whowechina/iidx_teeny/cad/iidx_keycap_teeny.stl

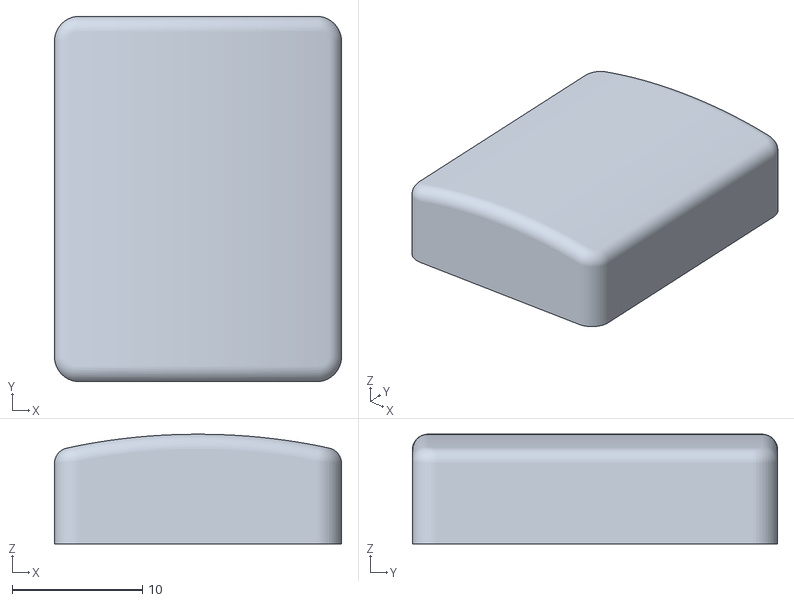
[picture p23: CAD file, 2023-05-01]
cad/iidx_keycap_teeny.stl
22.0 x 28.0 x 8.40
