whowechina/iidx_teeny/PCB/Keyboard/3dmodels/WS2812B.step

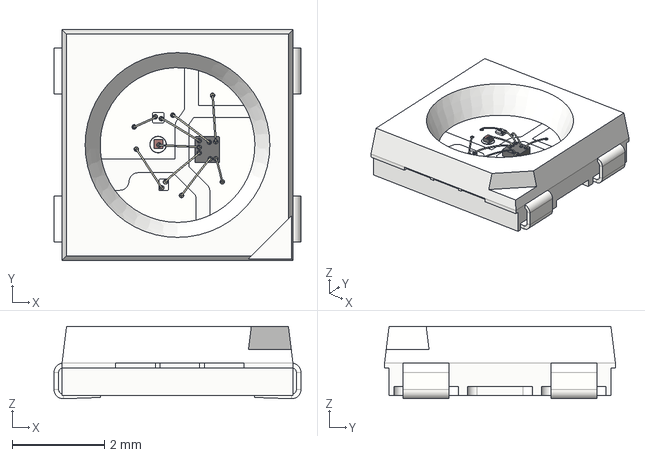
[picture p24: CAD file, 2023-05-01]
PCB/Keyboard/3dmodels/WS2812B.step
5.35 x 5.00 x 1.57 mm
