whowechina/iidx_teeny/Production/3DPrint/Keyboard Teeny - Panel.stl

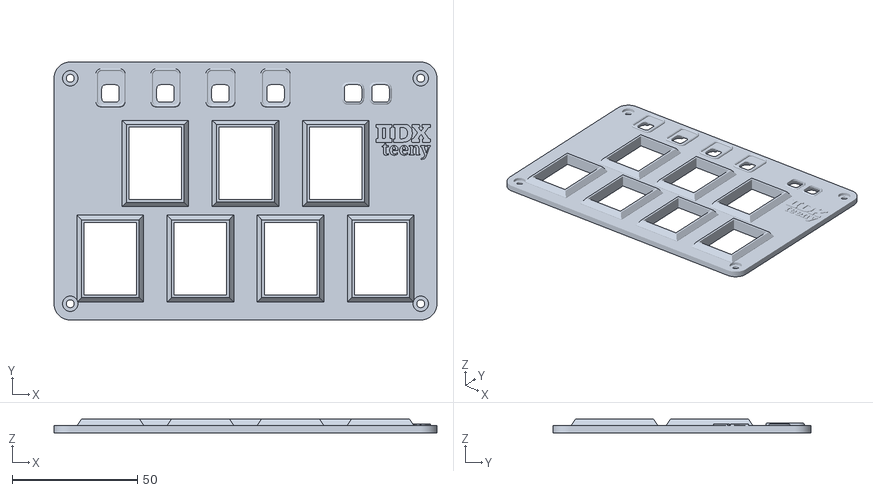
[picture p25: CAD file, 2024-12-18]
Production/3DPrint/Keyboard Teeny - Panel.stl
153.2 x 103.2 x 5.80
