whowechina/iidx_teeny/cad/nsk6804.stl

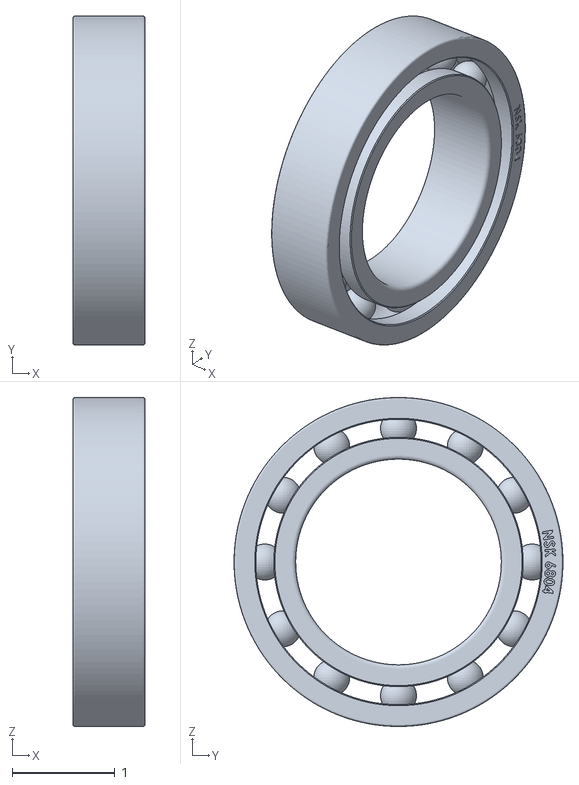
[picture p26: CAD file, 2023-05-01]
cad/nsk6804.stl
0.7 x 3.20 x 3.20
