whowechina/iidx_teeny/PCB/Keyboard/3dmodels/User Library-WS2812-2020.step

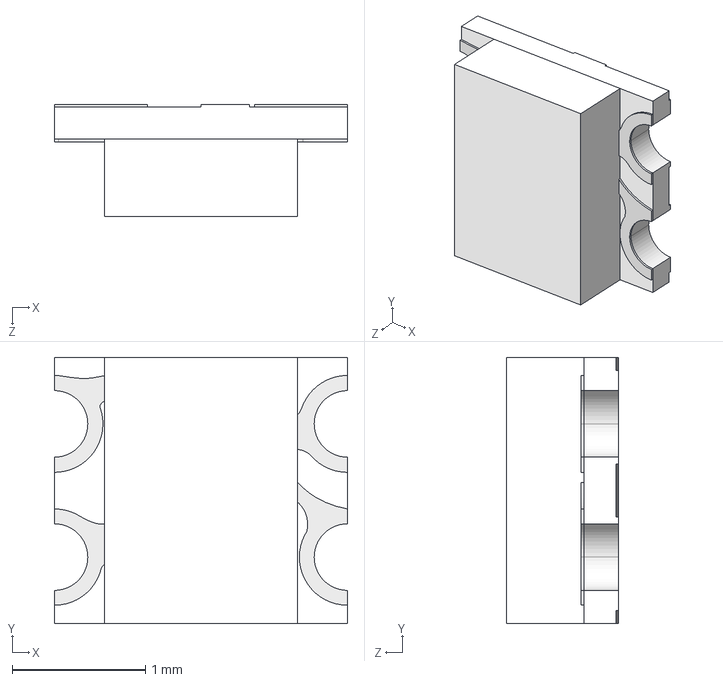
[picture p27: CAD file, 2023-05-01]
PCB/Keyboard/3dmodels/User Library-WS2812-2020.step
2.20 x 2.00 x 0.84 mm
