whowechina/iidx_teeny/cad/tt_led_ring_180.stl

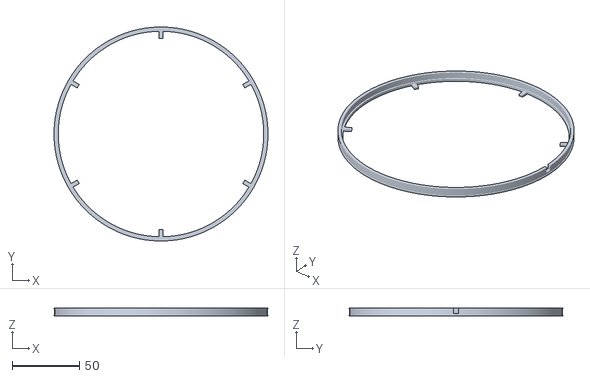
[picture p28: CAD file, 2023-05-01]
cad/tt_led_ring_180.stl
159.0 x 159.0 x 6.18
