whowechina/iidx_teeny/PCB/Keyboard/3dmodels/WS2812-0807.STEP

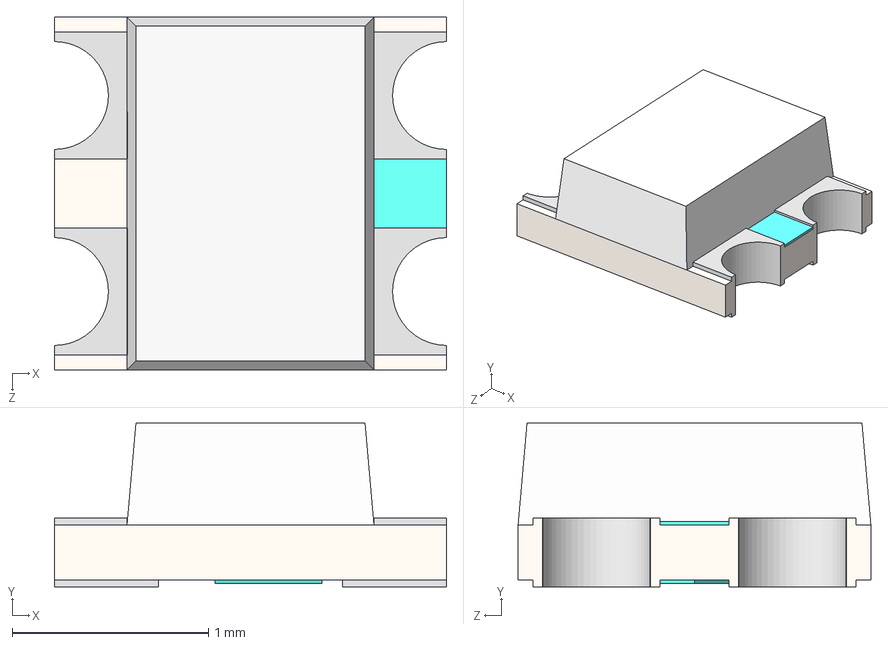
[picture p29: CAD file, 2023-05-01]
PCB/Keyboard/3dmodels/WS2812-0807.STEP
2.00 x 0.835 x 1.80 mm
