whowechina/iidx_teeny/Production/3DPrint/Turntable Teeny - Base.stl

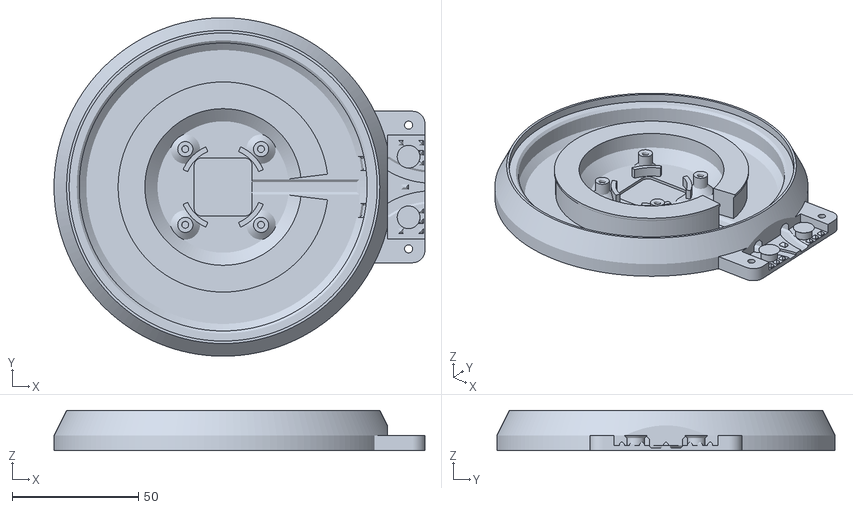
[picture p30: CAD file, 2024-12-18]
Production/3DPrint/Turntable Teeny - Base.stl
146.9 x 134.0 x 16.0
