whowechina/iidx_teeny/cad/keycap_frame_aux.stl

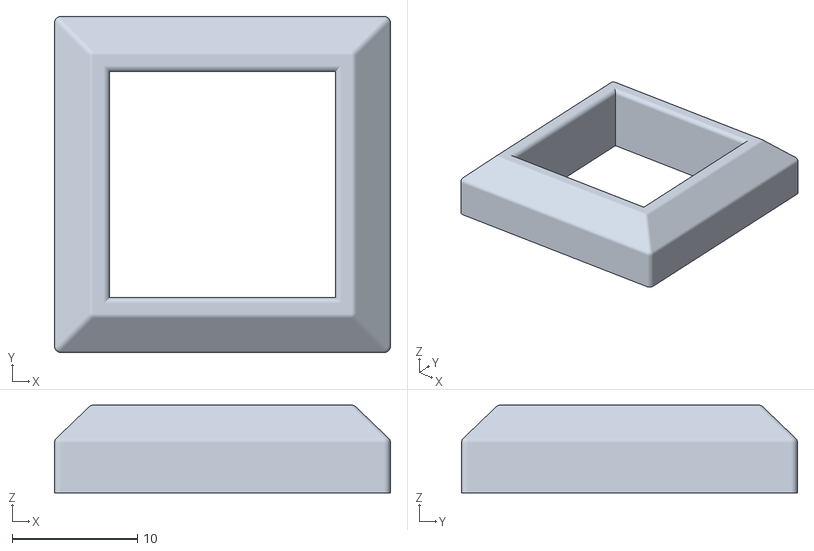
[picture p31: CAD file, 2023-05-01]
cad/keycap_frame_aux.stl
26.8 x 26.8 x 7.00
