whowechina/iidx_teeny/PCB/Keyboard/3dmodels/Magnetic Pogo Connector 5 Pin (F).STEP

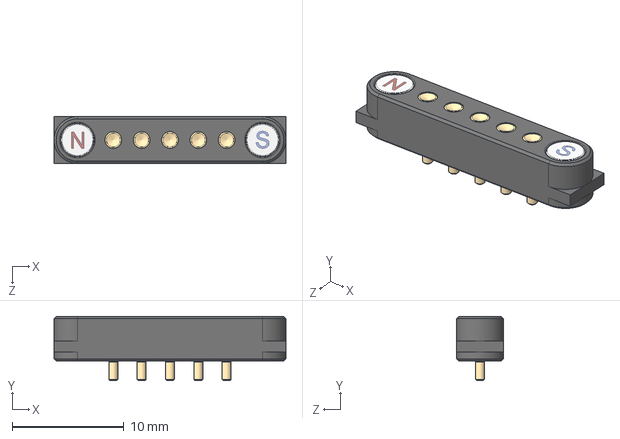
[picture p32: CAD file, 2023-05-01]
PCB/Keyboard/3dmodels/Magnetic Pogo Connector 5 Pin (F).STEP
20.8 x 5.75 x 4.20 mm
