whowechina/iidx_teeny/Production/3DPrint/Keyboard Teeny - Base_1P.stl

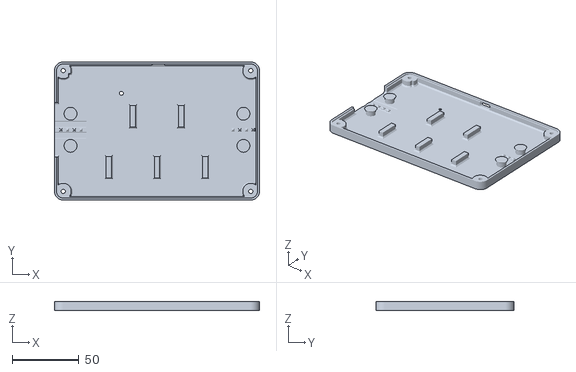
[picture p33: CAD file, 2024-12-18]
Production/3DPrint/Keyboard Teeny - Base_1P.stl
153.2 x 103.2 x 7.00
