whowechina/iidx_teeny/PCB/Keyboard/3dmodels/User Library-PTS645SL95SMTR92-LFS.STEP

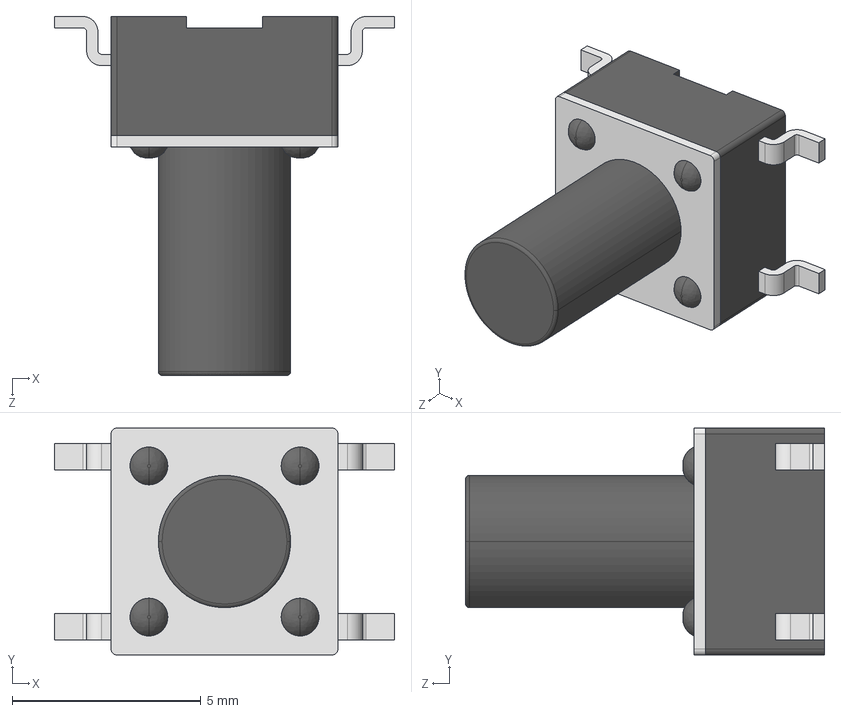
[picture p34: CAD file, 2023-05-01]
PCB/Keyboard/3dmodels/User Library-PTS645SL95SMTR92-LFS.STEP
9.00 x 6.00 x 9.50 mm
