whowechina/iidx_teeny/Production/3DPrint/Keycap Teeny - Choc V2.stl

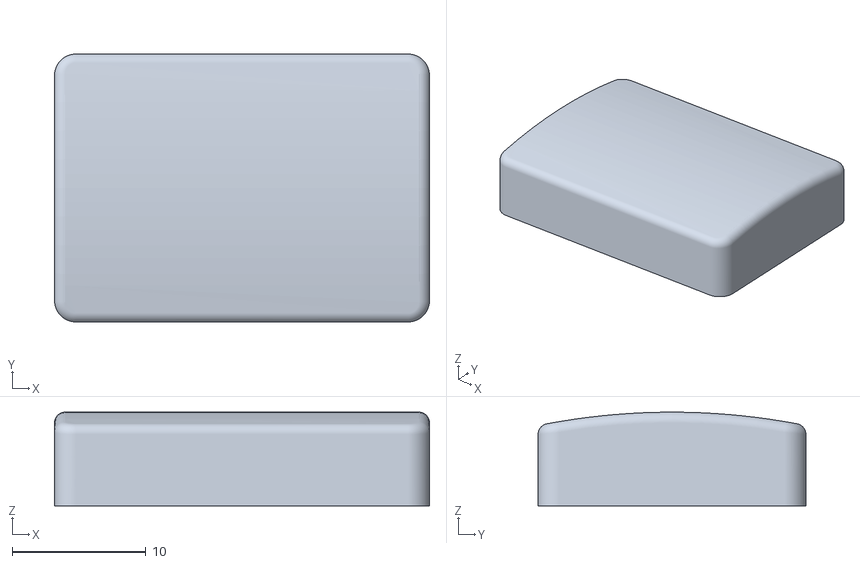
[picture p35: CAD file, 2024-12-18]
Production/3DPrint/Keycap Teeny - Choc V2.stl
28.0 x 20.0 x 7.00
