whowechina/iidx_teeny/cad/beatmania_iidx.stl

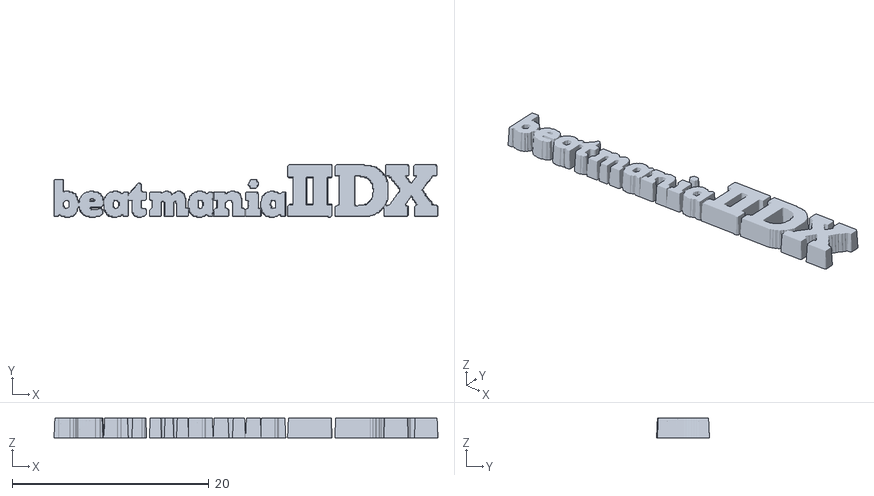
[picture p36: CAD file, 2023-05-01]
cad/beatmania_iidx.stl
39.0 x 5.38 x 2.00
