whowechina/iidx_teeny/PCB/Keyboard/3dmodels/EVQ-P1D05M.stp

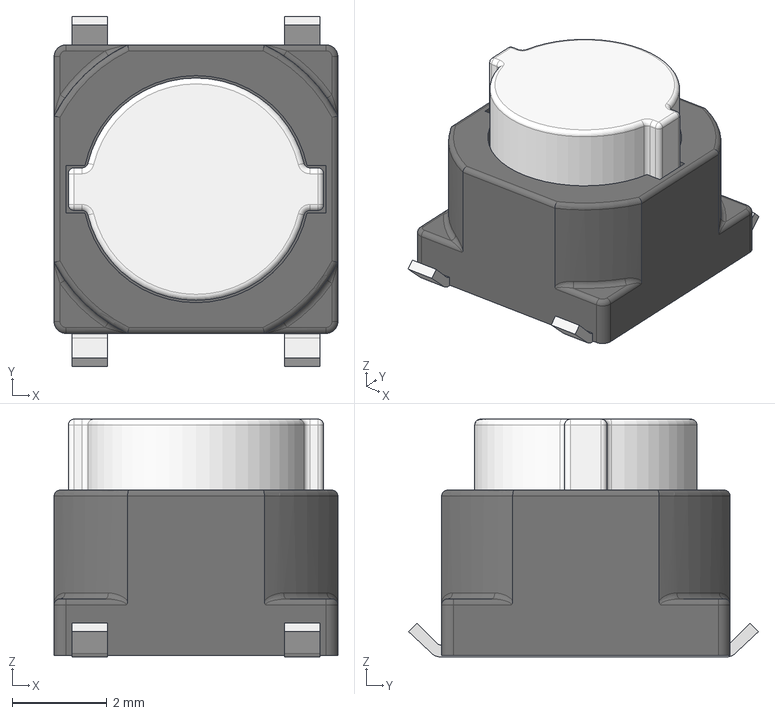
[picture p37: CAD file, 2023-05-01]
PCB/Keyboard/3dmodels/EVQ-P1D05M.stp
6.00 x 7.40 x 5.03 mm
