whowechina/iidx_teeny/PCB/Keyboard/3dmodels/WS2812-2020.STEP

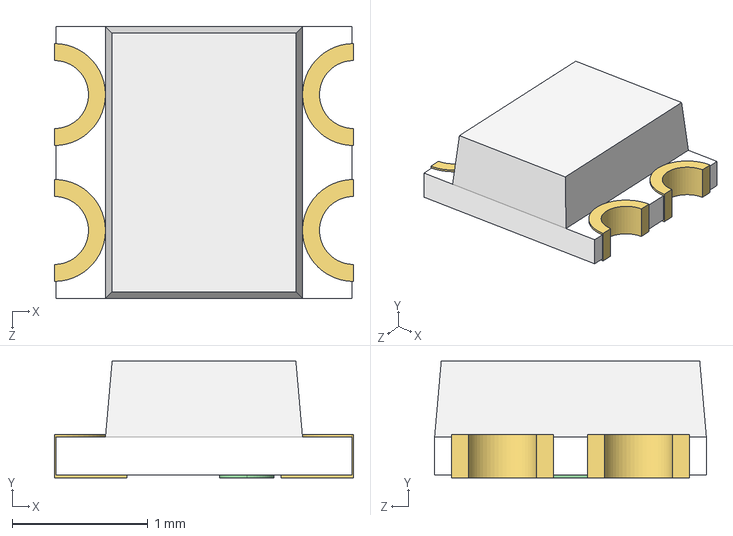
[picture p38: CAD file, 2023-05-01]
PCB/Keyboard/3dmodels/WS2812-2020.STEP
2.20 x 0.86 x 2.00 mm
