whowechina/iidx_teeny/Production/3DPrint/teeny_bottom_P2.stl

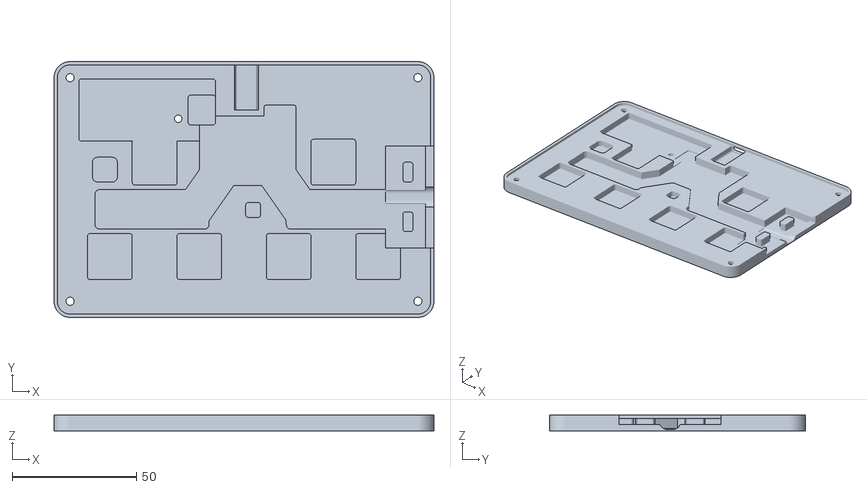
[picture p39: CAD file, 2024-02-12]
Production/3DPrint/teeny_bottom_P2.stl
153.0 x 103.0 x 6.40
