whowechina/iidx_teeny/cad/skf6805.stl

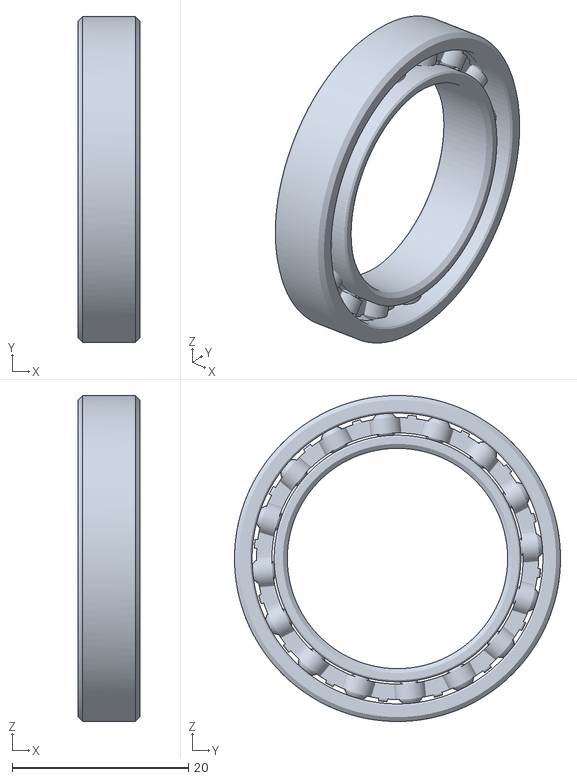
[picture p40: CAD file, 2023-05-01]
cad/skf6805.stl
7.00 x 37.0 x 37.0
