whowechina/iidx_teeny/PCB/Keyboard/3dmodels/SW_Hotswap_Kailh_MX.stp

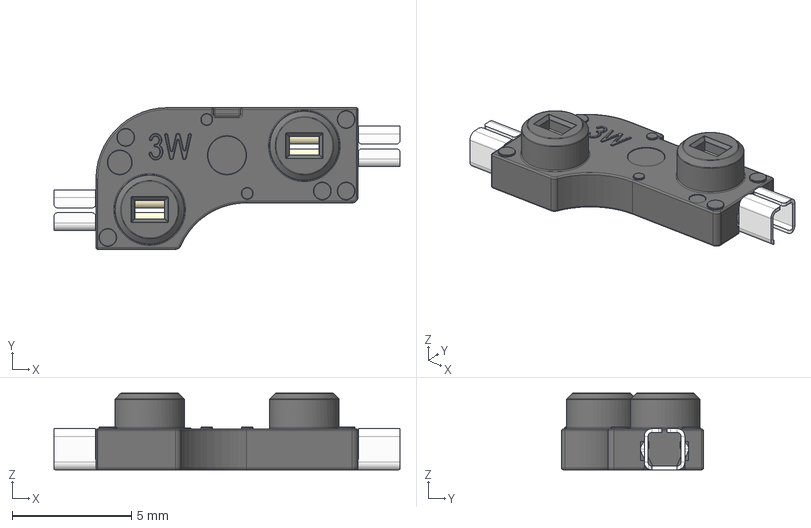
[picture p41: CAD file, 2023-05-01]
PCB/Keyboard/3dmodels/SW_Hotswap_Kailh_MX.stp
14.5 x 5.95 x 3.22 mm
