whowechina/iidx_teeny/cad/iidx_tt v1.stl

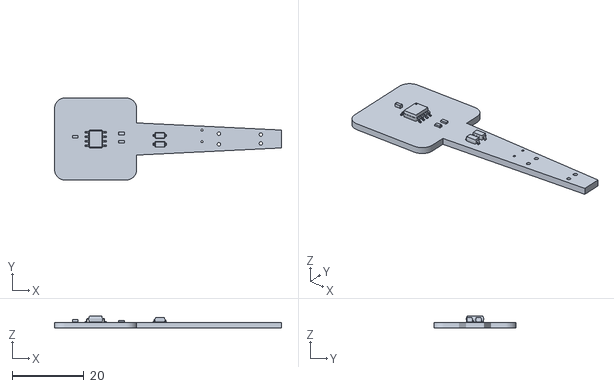
[picture p42: CAD file, 2023-05-01]
cad/iidx_tt v1.stl
63.5 x 23.0 x 3.40
