whowechina/iidx_teeny/PCB/Keyboard/3dmodels/Magnetic Pogo Connector 5 Pin (Type 2).STEP

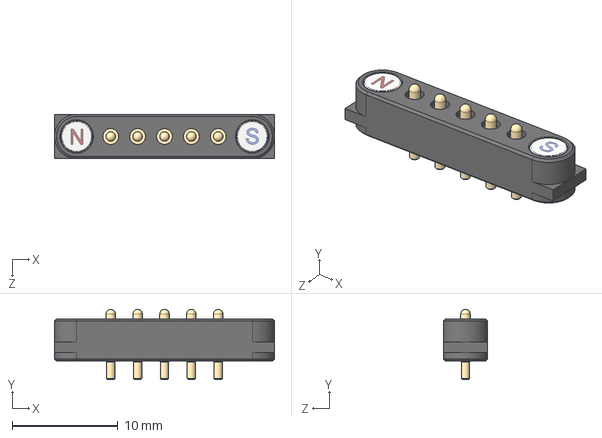
[picture p43: CAD file, 2023-05-01]
PCB/Keyboard/3dmodels/Magnetic Pogo Connector 5 Pin (Type 2).STEP
20.8 x 6.65 x 4.20 mm
