whowechina/iidx_teeny/Production/3DPrint/teeny_hinge_cover.stl

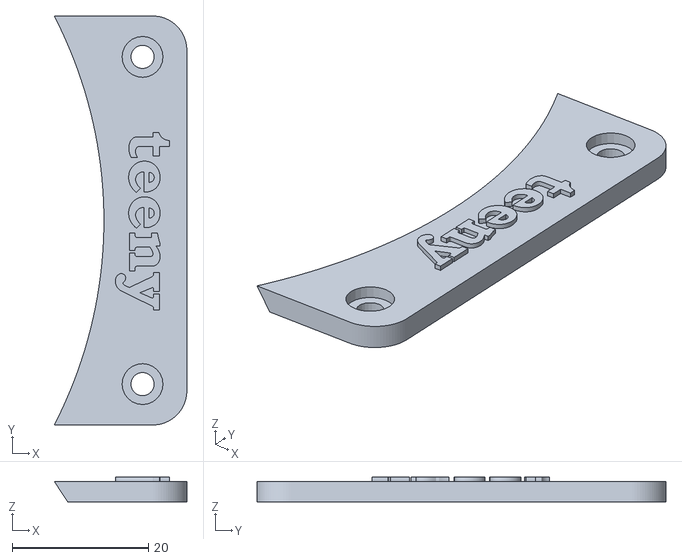
[picture p44: CAD file, 2023-07-23]
Production/3DPrint/teeny_hinge_cover.stl
19.5 x 60.0 x 3.60
