whowechina/iidx_teeny/PCB/Keyboard/3dmodels/SW_Kailh_Choc_V1.stp

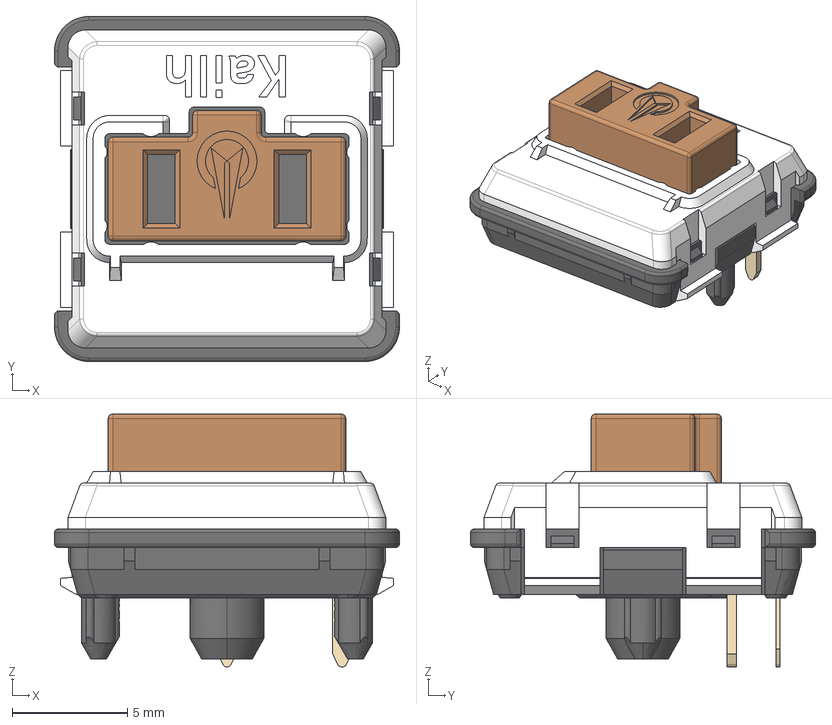
[picture p45: CAD file, 2023-05-01]
PCB/Keyboard/3dmodels/SW_Kailh_Choc_V1.stp
15.0 x 15.0 x 11.0 mm
