whowechina/iidx_teeny/Production/3DPrint/teeny_top.stl

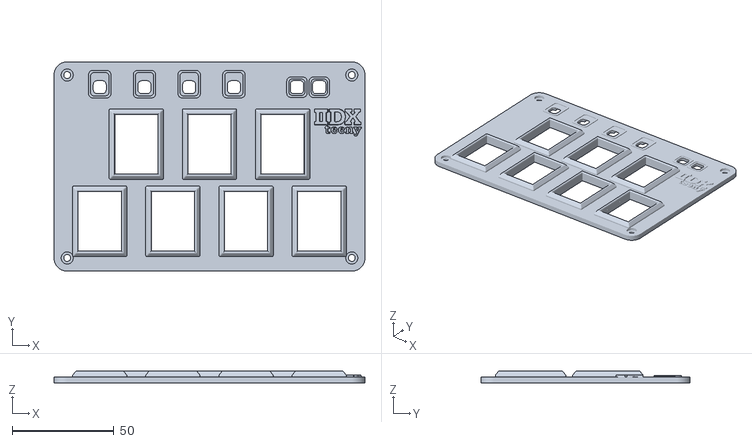
[picture p46: CAD file, 2023-05-26]
Production/3DPrint/teeny_top.stl
153.0 x 103.0 x 5.86
