whowechina/iidx_teeny/Production/3DPrint/teeny_keycap.stl

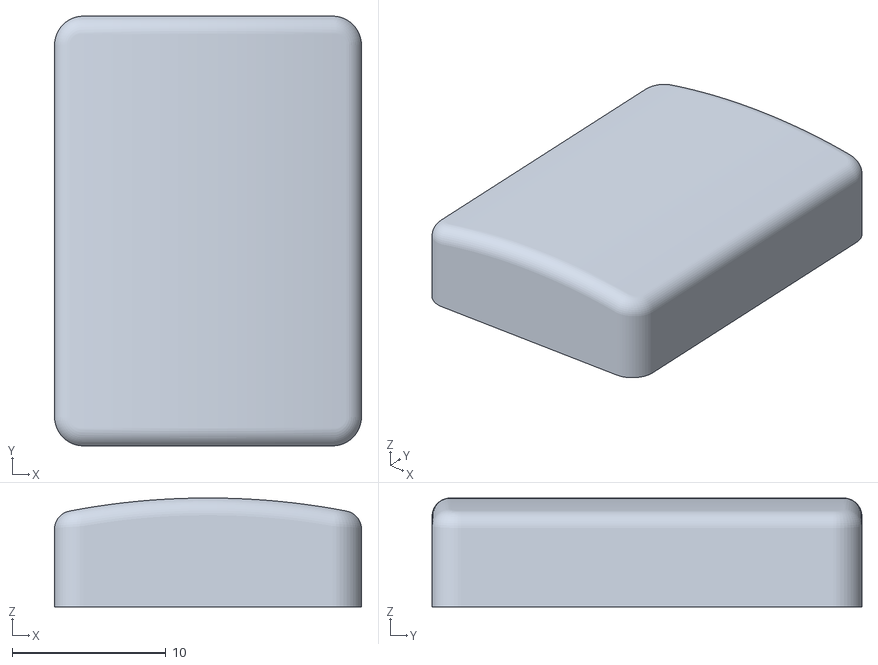
[picture p47: CAD file, 2023-05-21]
Production/3DPrint/teeny_keycap.stl
20.0 x 28.0 x 7.10
