whowechina/iidx_teeny/Production/3DPrint/teeny_disc.stl

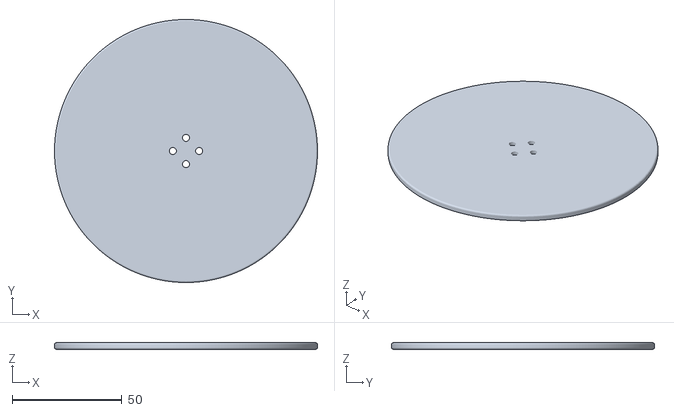
[picture p49: CAD file, 2023-05-14]
Production/3DPrint/teeny_disc.stl
120.0 x 120.0 x 2.99
