whowechina/iidx_teeny/PCB/Keyboard/3dmodels/SMD WS2812B-3535.step

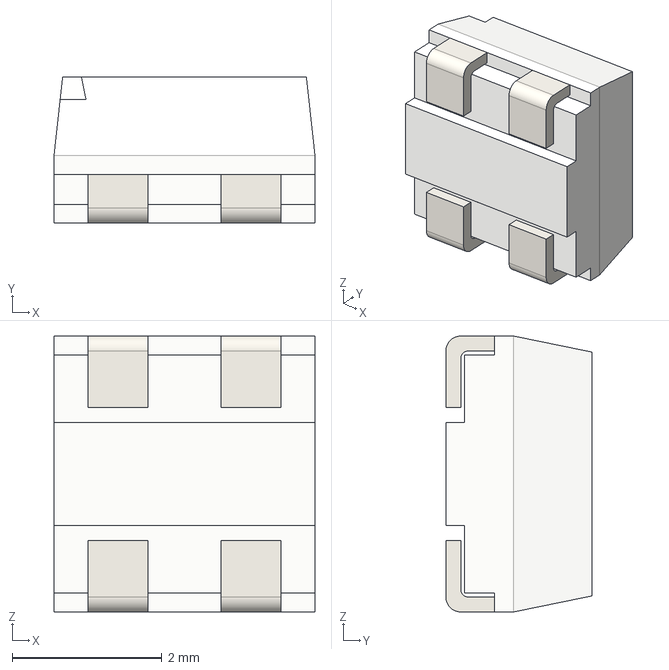
[picture p50: CAD file, 2023-05-01]
PCB/Keyboard/3dmodels/SMD WS2812B-3535.step
3.48 x 1.95 x 3.68 mm
