whowechina/iidx_teeny/Production/3DPrint/teeny_shaft.stl

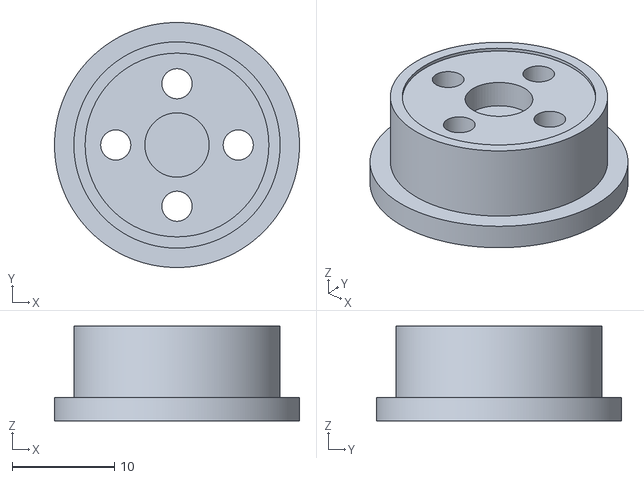
[picture p51: CAD file, 2023-05-14]
Production/3DPrint/teeny_shaft.stl
24.0 x 24.0 x 9.30
