whowechina/iidx_teeny/Production/3DPrint/teeny_bearing.stl

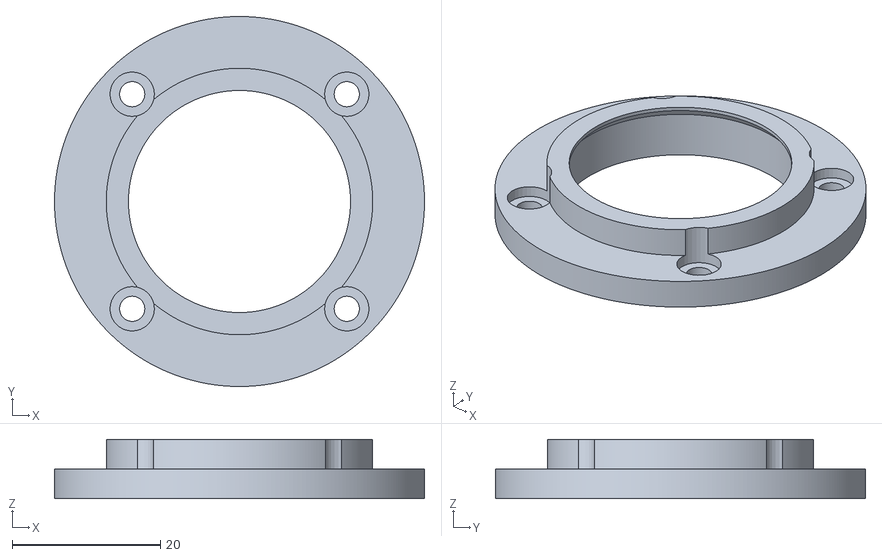
[picture p52: CAD file, 2023-05-14]
Production/3DPrint/teeny_bearing.stl
50.0 x 50.0 x 8.00
