whowechina/iidx_teeny/PCB/Keyboard/3dmodels/Magnetic Pogo Connector 5 Pin (Type 3).STEP

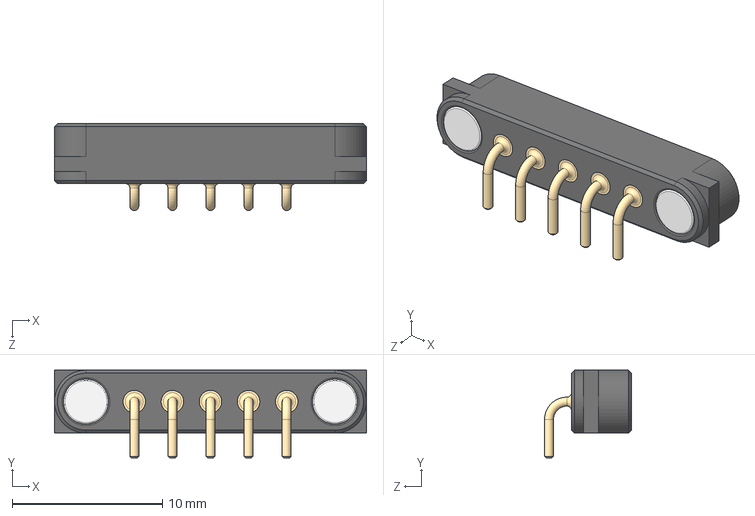
[picture p53: CAD file, 2023-05-01]
PCB/Keyboard/3dmodels/Magnetic Pogo Connector 5 Pin (Type 3).STEP
20.8 x 5.85 x 5.80 mm
