whowechina/iidx_teeny/PCB/Keyboard/3dmodels/Tact Switch 4.5mm SMT.step

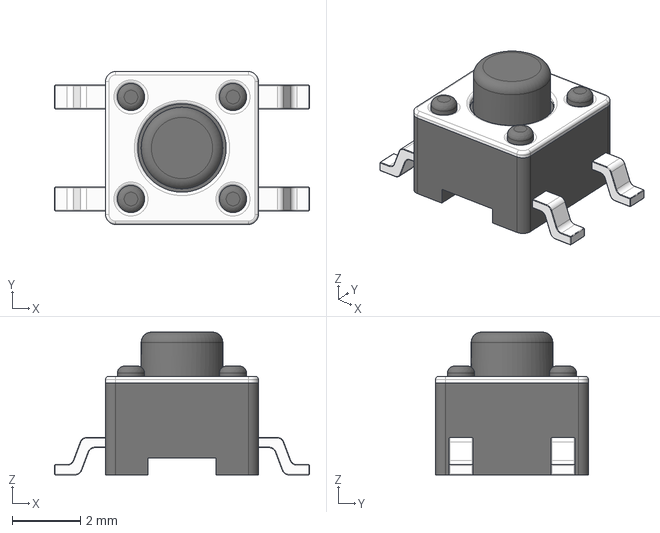
[picture p54: CAD file, 2023-05-01]
PCB/Keyboard/3dmodels/Tact Switch 4.5mm SMT.step
7.50 x 4.50 x 4.20 mm
