whowechina/iidx_teeny/PCB/Keyboard/3dmodels/Magnetic Pogo Connector 5 Pin (Type 4).STEP

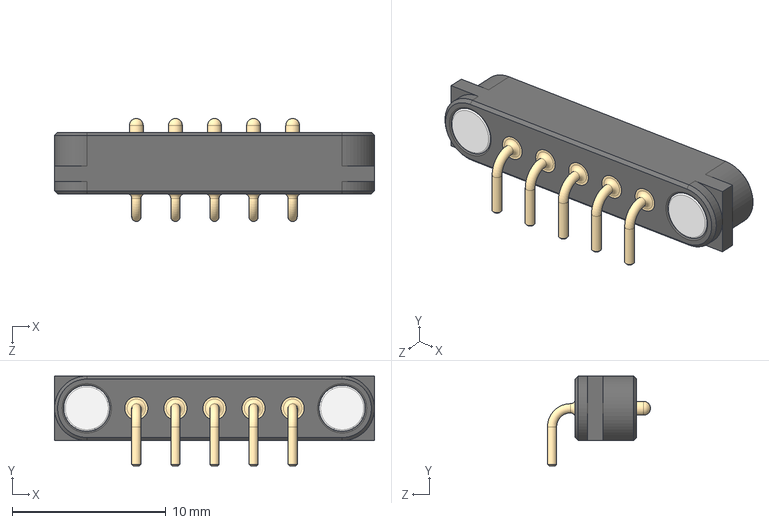
[picture p55: CAD file, 2023-05-01]
PCB/Keyboard/3dmodels/Magnetic Pogo Connector 5 Pin (Type 4).STEP
20.8 x 5.85 x 6.70 mm
